marekw1986/POLON7880/code/test/labels.asm

ABS EQU 0ca83H
AHOW EQU 0c687H
ASORRY EQU 0cbdcH
AWHAT EQU 0cbadH
BCD EQU 00001H
BIN EQU 00000H
BLKDAT EQU 0447cH
BLKENDL EQU 0467cH
BOOTCFSTR EQU 0cfa5H
BOOTMODESTR EQU 0cf93H
BOOTTBSTR EQU 0cfb7H
BOOT_CPM EQU 0cec2H
BOOT_MODE_INPUT EQU 0cea5H
BOOT_TINY_BASIC EQU 0ceddH
BUFEND EQU 04477H
BUFFER EQU 04437H
CFBASE EQU 00090H
CFCHERR EQU 0c067H
CFERRM EQU 0cf7aH
CFGETMBR EQU 0c0bcH
CFINFO EQU 0c0ddH
CFINIT EQU 0c010H
CFINIT_RET EQU 0c042H
CFLBA0 EQU 0447bH
CFLBA1 EQU 0447aH
CFLBA2 EQU 04479H
CFLBA3 EQU 04478H
CFMSG1 EQU 0cf58H
CFNERR EQU 0c07eH
CFR32SECTORS EQU 0c116H
CFREAD EQU 0c07fH
CFREADE EQU 0c090H
CFREG0 EQU 00090H
CFREG1 EQU 00091H
CFREG2 EQU 00092H
CFREG3 EQU 00093H
CFREG4 EQU 00094H
CFREG5 EQU 00095H
CFREG6 EQU 00096H
CFREG7 EQU 00097H
CFRSECT EQU 0c0feH
CFSLBA EQU 0c0a3H
CFWAIT EQU 0c043H
CFWAIT_TMOUT EQU 0c04bH
CFWAIT_TMOUT_LOOP_EXT EQU 0c04dH
CFWAIT_TMOUT_LOOP_INT EQU 0c04fH
CFWAIT_TMOUT_NOK EQU 0c064H
CFWAIT_TMOUT_OK EQU 0c061H
CFWRITE EQU 0c091H
CFWRITEE EQU 0c0a2H
CFWSECT EQU 0c12eH
CHARS EQU 0d0d3H
CHARS_END EQU 0d3d3H
CHECK_PARTITION1_SIZE EQU 0ce54H
CHGSGN EQU 0cb5eH
CHKIO EQU 0cf19H
CHKSGN EQU 0cb5bH
CI1 EQU 0cf36H
CK1 EQU 0cb76H
CKHLDE EQU 0cb70H
COMP EQU 0c601H
CONF_8255 EQU 00023H
CONTR_W_8253 EQU 00063H
COUNTER_LATCHING EQU 00000H
COUNT_REG_0_8253 EQU 00060H
COUNT_REG_1_8253 EQU 00061H
COUNT_REG_2_8253 EQU 00062H
CR EQU 0000dH
CRLF EQU 0c5efH
CURRNT EQU 00212H
CURSOR EQU 04686H
DEFLT EQU 0c936H
DELAY EQU 0c51eH
DIRECT EQU 0d46fH
DIVIDE EQU 0cb3eH
DV1 EQU 0cb49H
DV2 EQU 0cb4bH
ENDCHK EQU 0cba6H
ENDLESS_LOOP EQU 0c594H
ERROR EQU 0cbb0H
EX0 EQU 0d472H
EX1 EQU 0d476H
EX2 EQU 0d489H
EX3 EQU 0d493H
EX4 EQU 0d495H
EX5 EQU 0d49aH
EXEC EQU 0d472H
EXPR EQU 0c5f9H
EXPR1 EQU 0c94aH
EXPR2 EQU 0c98eH
EXPR3 EQU 0c9caH
EXPR4 EQU 0ca2eH
FI1 EQU 0cb9cH
FI2 EQU 0cba5H
FIN EQU 0cb93H
FINISH EQU 0c611H
FL1 EQU 0cc2eH
FL2 EQU 0cc45H
FNDLN EQU 0cc26H
FNDLP EQU 0cc2eH
FNDNXT EQU 0cc44H
FNDSKP EQU 0cc46H
FOR EQU 0c7f7H
FR1 EQU 0c807H
FR2 EQU 0c813H
FR3 EQU 0c819H
FR4 EQU 0c81cH
FR5 EQU 0c81fH
FR7 EQU 0c834H
FR8 EQU 0c855H
GETLN EQU 0cbe2H
GET_CFINFO EQU 0ce05H
GL1 EQU 0cbe8H
GL3 EQU 0cc0fH
GL4 EQU 0cc1eH
GOSUB EQU 0c7baH
GOTO EQU 0c74bH
HEXDUMP EQU 0c598H
HEXDUMP32BITVAL EQU 0c5caH
HEXDUMP32BITVAL_PLUS_SPACE EQU 0c5deH
HEXDUMP_A EQU 0c5aaH
HEXDUMP_NIB EQU 0c5bdH
HEXDUMP_NUM EQU 0c5c6H
HOW EQU 0c68dH
IFF EQU 0c8c1H
IGNBLK EQU 0c609H
INIT EQU 0cd46H
INP EQU 0cadaH
INPERR EQU 0c8d2H
INPIO EQU 0020eH
INPIO_ROM EQU 0cf49H
INPUT EQU 0c8dcH
IP1 EQU 0c8dcH
IP2 EQU 0c8ecH
IP3 EQU 0c8feH
IP4 EQU 0c92aH
IP5 EQU 0c933H
IR0_VECT EQU 0d4efH
IR1_VECT EQU 0ffe4H
IR2_VECT EQU 0ffe8H
IR3_VECT EQU 0ffecH
IR4_VECT EQU 0fff0H
IR5_VECT EQU 0fff4H
IR6_VECT EQU 0fff8H
IR7_VECT EQU 0fffcH
ISZERO32BIT EQU 0c581H
KBD2ASCII EQU 0c46cH
KBD2A_CHKKRSETSF EQU 0c4d1H
KBD2A_CHKSFT EQU 0c47fH
KBD2A_CHKSHFFLSET EQU 0c4b1H
KBD2A_CLRDATA_RETURN EQU 0c4e9H
KBD2A_CLRFLDATA_RETURN EQU 0c4e1H
KBD2A_CLRKRFL EQU 0c4a9H
KBD2A_LOOKUP EQU 0c4c1H
KBD2A_SVNEWDATA EQU 0c489H
KBDCRTLSET EQU 0c3d9H
KBDDATA EQU 04681H
KBDINIT EQU 0c3c9H
KBDKRFL EQU 04682H
KBDMSG EQU 0d012H
KBDNEW EQU 04685H
KBDOLD EQU 04684H
KBDSCANTABLE EQU 0c4efH
KBDSCANTABLE_FOUND EQU 0c50dH
KBDSCANTABLE_LOOP EQU 0c4f4H
KBDSCANTABLE_REL EQU 0c507H
KBDSFFL EQU 04683H
KBDWAITINBUF EQU 0c45cH
KBDWAITOUTBUF EQU 0c464H
KBD_CMD EQU 000a1H
KBD_DATA EQU 000a0H
KBD_ISR EQU 0d4b0H
KBD_ISR_RET EQU 0d4b8H
KBD_STATUS EQU 000a1H
LET EQU 0c93cH
LF EQU 0000aH
LIST EQU 0c75cH
LOAD_BASE EQU 00000H
LOAD_PARTITION1 EQU 0c1efH
LOG_FAULTY_MBR EQU 0ce1eH
LOG_PARTITION_TABLE EQU 0ce2cH
LOPINC EQU 0021cH
LOPLMT EQU 0021eH
LOPLN EQU 00220H
LOPPT EQU 00222H
LOPVAR EQU 0021aH
LS1 EQU 0c765H
LSTROM EQU 00000H
LT1 EQU 0c947H
MBRERRORSTR EQU 0cfcbH
MC_LOOP EQU 0c52eH
MD1 EQU 0ccfaH
MEMCOPY EQU 0c52bH
MISSINGPART1ERROR EQU 0cfddH
MISSINGSTR EQU 0cf62H
MODE_0 EQU 00000H
MODE_1 EQU 00002H
MODE_2 EQU 00004H
MODE_3 EQU 00006H
MODE_4 EQU 00008H
MODE_5 EQU 0000aH
MSG1 EQU 0cf4dH
MVDOWN EQU 0ccf2H
MVUP EQU 0cce7H
NEW EQU 0c71dH
NEWLINE EQU 0c549H
NEXT EQU 0c85cH
NEXTLINE EQU 0c38eH
NLDIV40INCR EQU 0c39fH
NLDIV40L EQU 0c39bH
NLDIV40SKIP EQU 0c3a3H
NLDIV40STORE EQU 0c3aaH
NLMUL40L EQU 0c3b4H
NX0 EQU 0c865H
NX1 EQU 0c8a1H
NX2 EQU 0c8b7H
NX3 EQU 0c87fH
NX4 EQU 0c891H
NX5 EQU 0c8b5H
OC2 EQU 0cefdH
OC3 EQU 0cf02H
OCSW EQU 00200H
OK EQU 0c692H
OUTC EQU 0c5f1H
OUTCMD EQU 0ca99H
OUTIO EQU 00201H
OUTIO_ROM EQU 0cf3cH
OUT_CHAR EQU 0c512H
PARN EQU 0ca45H
PARTMS EQU 0cf6aH
PASPRM EQU 0cb22H
PATLOP EQU 0cee0H
PA_8255 EQU 00020H
PB_8255 EQU 00021H
PC_8255 EQU 00022H
PEEK EQU 0cb03H
PETLA_DEL_WEWN EQU 0c520H
PIC_8259_HIGH EQU 000b1H
PIC_8259_LOW EQU 000b0H
PL_CHARS EQU 0d3d3H
PL_CHARS_END EQU 0d3d3H
PN1 EQU 0cc99H
PN2 EQU 0cca0H
PN3 EQU 0ccb0H
PN4 EQU 0ccb1H
PN5 EQU 0ccbfH
PN6 EQU 0ccc5H
POKE EQU 0cae9H
POPA EQU 0cd01H
PORT_8212 EQU 00000H
PP1 EQU 0cd1bH
PR0 EQU 0c78cH
PR1 EQU 0c798H
PR2 EQU 0c781H
PR3 EQU 0c79eH
PR6 EQU 0c7a9H
PR8 EQU 0c7afH
PRINT EQU 0c774H
PRINT_BOOT_OPTIONS EQU 0ce83H
PRNSTR EQU 0c55aH
PRN_IND_DIGIT EQU 0c539H
PRN_PARTITION_TABLE EQU 0c146H
PRN_ZERO_EX EQU 0c54fH
PRTLN EQU 0ccd2H
PRTNUM EQU 0cc8eH
PRTSTG EQU 0cc50H
PS1 EQU 0cc51H
PS2_SCANCODES EQU 0d3d3H
PS2_SCANCODES_END EQU 0d46fH
PU1 EQU 0cd43H
PUSHA EQU 0cd1dH
QHOW EQU 0c686H
QSORRY EQU 0cbdbH
QT1 EQU 0cc65H
QT2 EQU 0cc6eH
QT3 EQU 0cc72H
QT4 EQU 0cc7cH
QT5 EQU 0cc8dH
QTSTG EQU 0cc5eH
QWHAT EQU 0cbacH
RA1 EQU 0ca73H
RANPNT EQU 00224H
REM EQU 0c8bdH
RETURN EQU 0c7dcH
RL_LSB_ONLY EQU 00010H
RL_LSB_THEN_MSB EQU 00030H
RL_MSB_ONLY EQU 00020H
RND EQU 0ca56H
RSTART EQU 0c6a1H
RTCTICK EQU 0467fH
RTC_10_DAY_REG EQU 00087H
RTC_10_HOUR_REG EQU 00085H
RTC_10_MIN_REG EQU 00083H
RTC_10_MON_REG EQU 00089H
RTC_10_SEC_REG EQU 00081H
RTC_10_YEAR_REG EQU 0008bH
RTC_1_DAY_REG EQU 00086H
RTC_1_HOUR_REG EQU 00084H
RTC_1_MIN_REG EQU 00082H
RTC_1_MON_REG EQU 00088H
RTC_1_SEC_REG EQU 00080H
RTC_1_YEAR_REG EQU 0008aH
RTC_CTRLD_REG EQU 0008dH
RTC_CTRLE_REG EQU 0008eH
RTC_CTRLF_REG EQU 0008fH
RTC_ISR EQU 0d4d4H
RTC_WEEK_REG EQU 0008cH
RUN EQU 0c72cH
RUNNXL EQU 0c732H
RUNSML EQU 0c742H
RUNTSL EQU 0c73bH
RxRDY_MASK EQU 00002H
SCREEN_MAX_X EQU 0000aH
SCREEN_MAX_Y EQU 00018H
SEL_COUNTER_0 EQU 00000H
SEL_COUNTER_1 EQU 00040H
SEL_COUNTER_2 EQU 00080H
SETVAL EQU 0cb7aH
SET_PC EQU 0c003H
SIZE EQU 0ca8cH
SIZEPART1ERROR EQU 0cff8H
SIZESTR EQU 0cf8cH
SORRY EQU 0c69bH
SS1 EQU 0c609H
ST1 EQU 0c6a4H
ST2 EQU 0c6b4H
ST3 EQU 0c6bdH
ST4 EQU 0c6f4H
STACK EQU 07fffH
START EQU 0c007H
STARTADDRSTR EQU 0cf85H
STKGOS EQU 00214H
STKINP EQU 00218H
STKLMT EQU 04688H
STOP EQU 0c726H
SUBDE EQU 0cb54H
SV1 EQU 0cb90H
SWPSTR EQU 0c56dH
SYSTICK EQU 0467dH
TAB1 EQU 0d028H
TAB2 EQU 0d038H
TAB4 EQU 0d08dH
TAB5 EQU 0d0afH
TAB6 EQU 0d0b5H
TAB8 EQU 0d0bdH
TC1 EQU 0c64dH
TC2 EQU 0c658H
TIMER_ISR EQU 0d4bdH
TN1 EQU 0c663H
TRYKBINIT EQU 0cdd3H
TSTC EQU 0c5e7H
TSTNUM EQU 0c65cH
TSTV EQU 0c619H
TV1 EQU 0c63dH
TXTBGN EQU 00228H
TXTEND EQU 04400H
TXTUNF EQU 00226H
TxRDY_MASK EQU 00001H
UART_8251_CTRL EQU 00041H
UART_8251_DATA EQU 00040H
UART_RX_ISR EQU 0d4a0H
UART_TX_ISR EQU 0d4a8H
USR EQU 0cb0dH
USRET EQU 0cb38H
VARBGN EQU 04400H
VARNXT EQU 00216H
VDPCLCURSOR EQU 0c377H
VDPCLS EQU 0c260H
VDPINIT EQU 0c21aH
VDPPUTC EQU 0c2edH
VDPPUTC_BSDEC EQU 0c303H
VDPPUTC_CHCR EQU 0c316H
VDPPUTC_CHECKCURSOR EQU 0c33fH
VDPPUTC_CHECKCURSORLSB EQU 0c34bH
VDPPUTC_CHLF EQU 0c310H
VDPPUTC_RET EQU 0c360H
VDPPUTC_SEND EQU 0c322H
VDPRVRAM EQU 0c2d6H
VDPRVRAML EQU 0c2e0H
VDPSCROLLUP EQU 0c283H
VDPUTC_EXCEEDED EQU 0c353H
VDPWVRAM EQU 0c2bdH
VDPWVRAML EQU 0c2c9H
VDPZEROVRAM EQU 0c26aH
VDPZEROVRAML EQU 0c276H
VDP_DATA EQU 000a8H
VDP_ISR EQU 0d4e7H
VDP_MODE EQU 000a9H
WAITCM EQU 0cab7H
WAITIO EQU 00204H
WAITIO_ROM EQU 0cf3fH
WHAT EQU 0c695H
XP11 EQU 0c950H
XP12 EQU 0c956H
XP13 EQU 0c95cH
XP14 EQU 0c963H
XP15 EQU 0c96bH
XP16 EQU 0c971H
XP17 EQU 0c977H
XP18 EQU 0c979H
XP21 EQU 0c999H
XP22 EQU 0c99eH
XP23 EQU 0c9a1H
XP24 EQU 0c9aaH
XP25 EQU 0c9bbH
XP26 EQU 0c9c0H
XP31 EQU 0c9cdH
XP32 EQU 0c9ecH
XP33 EQU 0c9f4H
XP34 EQU 0c9ffH
XP35 EQU 0ca20H
XP40 EQU 0ca34H
XP41 EQU 0ca3fH
XP42 EQU 0ca52H
XP43 EQU 0ca53H
